johnyHV/GSM_Controll/FOTO/P_20200427_174748.jpg

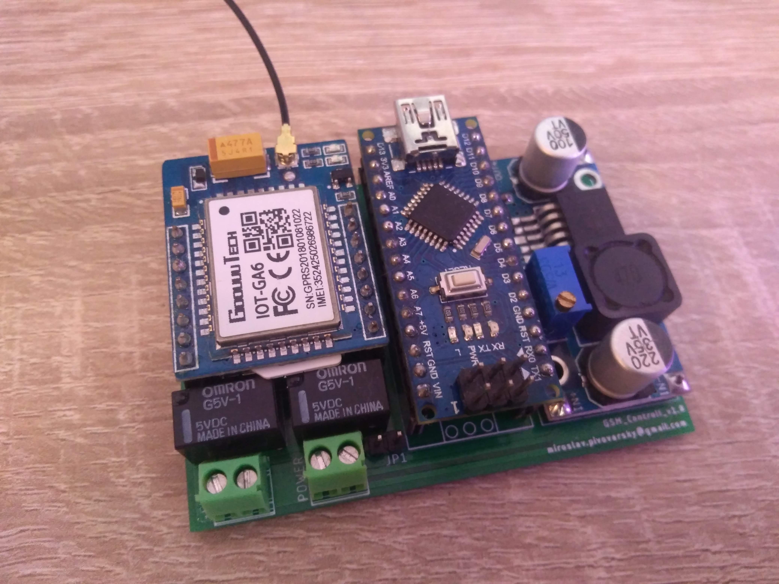
FOTO/P_20200427_174748.jpg
