johnyHV/GSM_Controll/GSM_Controll/HW_cfg.h

/**
 * @file HW_cfg.h
 *
 * @brief H - file s konfiguraciou MCU
 *
 * @author Miroslav Pivovarsky
 * Contact: miroslav.pivovarsky@gmail.com
 * 
 * @bug: no know bug
 *
 */

#ifndef __HW_CFG_H_
#define __HW_CFG_H_

#define SW_VERSION    "SW Version 1.0"// verzia SW  

#define GSM_A6_TX     10              // A6 TX
#define GSM_A6_RX     9               // A6 RX
#define GSM_A6_NET    5               // A6 Net status
#define GSM_A6_PWR    4               // A6 Power 
#define GSM_A6_INT    3               // A6 Interupt
#define GSM_A6_RST    2               // A6 Reset

#define RELE_A        6               // Rele A
#define RELE_B        7               // Rele B
#define INPUT_A       8               // Digitalny vstup

#define SYSTEM_E_NUM_MASTER     0
#define SYSTEM_E_NUM1_ADD       20
#define SYSTEM_E_NUM2_ADD       40
#define SYSTEM_E_NUM3_ADD       60
#define SYSTEM_E_NUM4_ADD       80
#define SYSTEM_E_NUM5_ADD       100
#define SYSTEM_E_NUM6_ADD       120
#define SYSTEM_E_NUM7_ADD       140
#define SYSTEM_E_NUM8_ADD       160
#define SYSTEM_E_NUM9_ADD       180
#define SYSTEM_E_NUM10_ADD      200
#define SYSTEM_E_NUM11_ADD      220
#define SYSTEM_E_NUM12_ADD      240
#define SYSTEM_E_NUM13_ADD      260
#define SYSTEM_E_NUM14_ADD      280
#define SYSTEM_E_NUM15_ADD      300
#define SYSTEM_E_NUM16_ADD      320
#define SYSTEM_E_NUM17_ADD      340
#define SYSTEM_E_NUM18_ADD      360
#define SYSTEM_E_NUM19_ADD      380
#define SYSTEM_E_NUM20_ADD      400

#endif
